Rhetticle/Ruthless-RFID/Firmware/Ruthless RFID/Core/Src/MFRC.c

/*
 * MFRC.c
 *
 *  Created on: Jan 30, 2024
 *      Author: rhett
 */


#include "MFRC.h"
#include "stm32f4xx.h"
#include "usbd_cdc_if.h"
#include "OLED.h"
#include "ruthlessfs.h"

extern I2C_HandleTypeDef hi2c1;



/* Write single byte MFRC register
 *
 * @param addr: register address
 *
 * @param data: value to write to register
 */

PCD_StatusTypeDef MFRC_REGW(uint8_t addr,uint8_t data){
	uint8_t value=data;
	if(HAL_I2C_Mem_Write(&hi2c1, MFRC_ADDR<<1, addr, 1, &value, 1, 100)!=HAL_OK){
		return(PCD_I2C_ERR);
	}
	else{
		return(PCD_OK);
	}
	HAL_Delay(1);
}

/* Read single byte from MFRC register
 *
 * @param addr: register address
 *
 * @param data: pointer to store read value
 */

PCD_StatusTypeDef MFRC_REGR(uint8_t addr,uint8_t* data){
	if(HAL_I2C_Mem_Read(&hi2c1, MFRC_ADDR<<1, addr, 1, data, 1, 100)!=HAL_OK){
		return(PCD_I2C_ERR);
	}
	else{
		return(PCD_OK);
	}
	HAL_Delay(1);
}

/* Write to MFRC FIFO buffer
 *
 * @param data: Array of data to write to FIFO
 *
 * @param size: Size of array (bytes)
 */

PCD_StatusTypeDef MFRC_FIFOW(uint8_t* data,uint8_t size){
	for(int i=0;i<size;i++){
		if(HAL_I2C_Mem_Write(&hi2c1, MFRC_ADDR<<1, 0x09, 1, &data[i], 1, 100)!=HAL_OK){
			return(PCD_I2C_ERR);

		}
		HAL_Delay(1);

	}
	return(PCD_OK);
}

/* Read from MFRC FIFO buffer
 *
 * @param data: Array to store read values (Ensure array is large enough)
 *
 * @param size: Number of bytes to read from FIFO
 */

PCD_StatusTypeDef MFRC_FIFOR(uint8_t* data,uint8_t size){
	for(int i=0;i<size;i++){
		if(HAL_I2C_Mem_Read(&hi2c1, MFRC_ADDR<<1, 0x09, 1, &data[i], 1, 100)!=HAL_OK){
			return(PCD_I2C_ERR);
		}
		HAL_Delay(1);

	}
	return(PCD_OK);
}

void MFRC_Test(void){
	uint8_t value;
	MFRC_REGR(0x37,&value); //Expect 0x91 or 0x92
	CDC_Transmit_FS(&value,1);
}

void MFRC_ANTON(void){
	uint8_t value;
	MFRC_REGR(TX_CONT, &value);
	if ((value & 0x03) != 0x03) {
		MFRC_REGW(TX_CONT, value | 0x03);
	}
}

void SET_ANTGAIN(void){
	uint8_t value;
	MFRC_REGR(RFCfgReg,&value);
	MFRC_REGW(RFCfgReg,value|0x70); //Set receiver gain to 48dB
}

void ClearBitMask(uint8_t addr,uint8_t mask){
	uint8_t tmp;
	MFRC_REGR(addr,&tmp);
	MFRC_REGW(addr,tmp&(~mask));
}

void MFRC_ANTOFF(void){
	ClearBitMask(TX_CONT,0x03);
}

/*
 * Function to calculate CRC on whatever data is in FIFO
 * !!CRCIRQ bit in DivIrqReg register can be used to detect when CRC has been calculated!!
 *
 * @param result: Array to store the two bytes of CRC
 *
 * */

PCD_StatusTypeDef CALC_CRC(uint8_t* data,uint8_t size,uint8_t* result){
	uint8_t CRCIRQ;
	MFRC_REGW(CMD_REG,IDLE); //clear command register
	MFRC_REGW(DIVIRQ,0x04); //Clear interrupt bits so we can detect when CRCIRQ is set
	MFRC_REGW(FIFO_LEV,0x80);
	MFRC_FIFOW(data, size); //Write data to FIFO ready for CRC calculation
	MFRC_REGW(CMD_REG,CALCCRC); //Execute CRC calculation command
	HAL_Delay(100);
	MFRC_REGR(DIVIRQ,&CRCIRQ);
	if((CRCIRQ&0x04)!=0x04){
		return(CRC_ERR); //CRC calculation took too long
	}
	MFRC_REGW(CMD_REG,IDLE);
	MFRC_REGR(CRCL, &result[0]);
	MFRC_REGR(CRCH, &result[1]); //Store the 16-bit CRC in result
	return(PCD_OK);

}

/* Initialise MFRC to begin transceiving
 *
 * Code is written to interface with MIFARE Ultralight PICC. Different PICCs will need different baud rate.
 */

PCD_StatusTypeDef MFRC_INIT(void){
	HAL_GPIO_WritePin(GPIOB, NRST, 1); //Make sure MFRC is not reset
	HAL_GPIO_WritePin(GPIOB, NRST, 0);
	HAL_Delay(1);
	HAL_GPIO_WritePin(GPIOB, NRST, 1);
	HAL_Delay(50);
	MFRC_REGW(TX_REG,0x00);
	MFRC_REGW(RX_REG,0x00);
	MFRC_REGW(MODWIDTH,0x26);
	MFRC_REGW(TXASK,0x40); //Force 100% ASK modulation regardless of ModGsPrereg
	MFRC_REGW(MODE_REG,0x3D);
	MFRC_ANTON();
	return(PCD_OK);



}


/* Transceive data between MFRC and PICC
 *
 * @param sendData: Array of data to send
 *
 * @param sendsize: Number of bytes to send
 *
 * @param recdata: Array to store received data
 *
 * @param recsize: Number of bytes to receive
 *
 * @param validbits: Number of valid bits within given byte in sendData
 *
 * !!Check PICC datasheet to see what data is needed in sendData i.e. Read/Write command, response bytes etc!!
 * !!When writing ensure correct address, most MIFARE PICCs contain OTP (one-time-programmable) sections as well as
 * lock bytes to remove write permissions from certain pages. These operations are NOT reversable!!
 */

PCD_StatusTypeDef MFRC_TRANSCEIVE(uint8_t* sendData,uint8_t sendsize,uint8_t* recdata,uint8_t recsize,uint8_t validbits){
	uint8_t IRQval=0;
	uint8_t BIT_val=0;

	MFRC_REGW(CMD_REG,IDLE); //Clear command register
	MFRC_REGW(IRQ_REG,0x7F);
	MFRC_REGW(FIFO_LEV,0x80); //Clear FIFO buffer
	MFRC_FIFOW(sendData,sendsize); //Write data to FIFO ready for transmission
	MFRC_REGW(BITFRAME,validbits);
	MFRC_REGW(CMD_REG,TRANSCEIVE); //Send FIFO data and receive PICC response
	MFRC_REGR(BITFRAME,&BIT_val);
	MFRC_REGW(BITFRAME,(BIT_val|0x80)); //Start send bit
	while(IRQval&0x30!=0x30){ //Hang here until RXIRQ and IDLEIRQ bits are set
		MFRC_REGR(IRQ_REG,&IRQval);
	}
	HAL_Delay(1);
	MFRC_FIFOR(recdata,recsize); //Read and store received data


	return(PCD_OK);
}

/*
 * Function to send a REQA to detect if a PICC is present
 *
 * @param response: Array to store response from PICC
 *
 * */

PCD_StatusTypeDef MFRC_REQA(uint8_t* response){
	uint8_t REQ=0x26;
	ClearBitMask(COLLREG, 0x80);
	if(MFRC_TRANSCEIVE(&REQ,1, response, 2, 7)!=PCD_OK){//REQA is a 7-bit command
		return(PCD_COMM_ERR);
	}

	else{
		return(PCD_OK);
	}
}

/*
 * Function to issue the WUPA command to PICC (We use this to go from HALT to READY state check ISO standard)
 *
 * @param reponse: PICC reponse to WUPA (Expect 0x44, 0x00 for ULTRALIGHT
 * */

PCD_StatusTypeDef MFRC_WUPA(uint8_t* response){
	uint8_t WUPA=0x52;
	ClearBitMask(COLLREG, 0x80);
	if(MFRC_TRANSCEIVE(&WUPA,1, response, 2, 7)!=PCD_OK){//WUPA is a 7-bit command
		return(PCD_COMM_ERR);
	}

	else{
		return(PCD_OK);
	}
}

/*
 * Function to issue HALTA command to PICC (Change from READY to HALT state) Send WUPA and select sequence to re-select PICC
 * */

PCD_StatusTypeDef MFRC_HALTA(void){
	uint8_t transaction[4]={ULTRA_HALTA,0x00};
	uint8_t CRC_val[2];
	uint8_t ack;

	if(CALC_CRC(transaction, 2, CRC_val)!=PCD_OK){
		return(CRC_ERR);
	}
	memcpy(transaction+2,CRC_val,2);

	if(MFRC_TRANSCEIVE(transaction, 4, &ack, 1, 0)!=PCD_OK){
		return(PCD_COMM_ERR);
	}

	else{
		return(PCD_OK);
	}
}

/*
 * Function to transceive anticollision cascade level 1 command (Second step after REQA to select PICC)
 *
 * @param response: Array to store PICC response to anticollision command
 * */

PCD_StatusTypeDef MFRC_ANTICOL1(uint8_t* reponse){
	uint8_t transaction[]={0x93,0x20};
	ClearBitMask(COLLREG, 0x80);
	if(MFRC_TRANSCEIVE(transaction, 2, reponse, 5, 0)!=PCD_OK){
		return(PCD_COMM_ERR);
	}
	else{
		return(PCD_OK);
	}
}

/*
 * Function to perform SELECT command (Cascade level 1)
 *
 * @param anticol: Data the is retrieved from MFRC_ANTICOL1
 *
 * @param response: Array to store PICC response to command (Expect SAK of 0x04 and two bytes CRC)
 *
 * */

PCD_StatusTypeDef MFRC_SEL1(uint8_t* anticol,uint8_t* response){
	uint8_t transaction[9]={0x93,0x70};
	uint8_t CRC_val[2];

	memcpy(transaction+2,anticol,5);
	CALC_CRC(transaction, 7, CRC_val);

	memcpy(transaction+7,CRC_val,2);

	if(MFRC_TRANSCEIVE(transaction, 9, response, 3, 0)!=PCD_OK){
		return(PCD_COMM_ERR);
	}

	else{
		return(PCD_OK);
	}

}

/*
 * Function to transceive anticollision cascade level 2 command (Cascade level 1 commands must be performed first)
 *
 * @param response: Array to store PICC response to anticollision command
 * */

PCD_StatusTypeDef MFRC_ANTICOL2(uint8_t* reponse){
	uint8_t transaction[]={0x95,0x20};
	ClearBitMask(COLLREG, 0x80);
	if(MFRC_TRANSCEIVE(transaction, 2, reponse, 5, 0)!=PCD_OK){
		return(PCD_COMM_ERR);
	}
	else{
		return(PCD_OK);
	}
}

/*
 * Function to perform SELECT command (Cascade level 2)
 *
 * @param anticol: Data the is retrieved from MFRC_ANTICOL2
 *
 * @param response: Array to store PICC response to command (Expect SAK of 0x00 and two bytes CRC)
 *
 * */

PCD_StatusTypeDef MFRC_SEL2(uint8_t* anticol,uint8_t* response){
	uint8_t transaction[9]={0x95,0x70};
	uint8_t CRC_val[2];

	memcpy(transaction+2,anticol,5);
	CALC_CRC(transaction, 7, CRC_val);

	memcpy(transaction+7,CRC_val,2);

	if(MFRC_TRANSCEIVE(transaction, 9, response, 3, 0)!=PCD_OK){
		return(PCD_COMM_ERR);
	}

	else{
		return(PCD_OK);
	}

}

/*
 * Function to select the MIFARE ULTRALIGHT PICC (Don't forget to call REQA on first power up or use PICC_CHECK below)
 * */

PCD_StatusTypeDef PICC_Select(void){
	  uint8_t ANTICOL1[5];
	  uint8_t SELECT1[3];
	  uint8_t ANTICOL2[5];
	  uint8_t SELECT2[3];
	  uint8_t ATQA[2];

	  if (PICC_CHECK() != PCD_OK) {
		  return PCD_COMM_ERR;
	  }
	  MFRC_WUPA(ATQA);
	  MFRC_ANTICOL1(ANTICOL1);
	  if(ANTICOL1[0]!=0x88){
		  return(PCD_COMM_ERR);
	  }
	  HAL_Delay(10);
	  MFRC_SEL1(ANTICOL1, SELECT1);
	  HAL_Delay(10);
	  MFRC_ANTICOL2(ANTICOL2);
	  HAL_Delay(10);
	  MFRC_SEL2(ANTICOL2, SELECT2);
	  HAL_Delay(10);
	  return(PCD_OK);
}

/*
 * Function to check for PICC in field
 * */

PCD_StatusTypeDef PICC_CHECK(void){
	uint8_t ATQA[2];
	if(MFRC_WUPA(ATQA)!=PCD_OK){
		return(PCD_COMM_ERR);
	}

	else{
		if((ATQA[0]!=ULTRA_ATQA0) || (ATQA[1] != ULTRA_ATQA1)){
			return(PCD_COMM_ERR);
		}
		else{
			MFRC_HALTA();
			return(PCD_OK);
		}
	}
}
/*
 * Function to read data from MIFARE ULTRALIGHT PICC
 *
 * @param addr: Start address (PICC will return data from first four pages)
 *
 * @param data: Array to store read data
 *
 * */

PCD_StatusTypeDef UL_READ(uint8_t addr,uint8_t* data){

	uint8_t transaction[4]={ULTRA_READ,addr};
	uint8_t CRC_val[2];

	CALC_CRC(transaction, 2, CRC_val);

	memcpy(transaction+2,CRC_val,2);

	if(MFRC_TRANSCEIVE(transaction, 4, data, UL_READSIZE, 0)!=PCD_OK){
		return(PCD_COMM_ERR);
	}

	else{
		return(PCD_OK);
	}
}

/*
 * Function to write 4 bytes (1 page) to MIFARE Ultralight PICC
 *
 * @param addr: Page start address
 *
 * @param data: Array of 4 bytes to write
 *
 * */

PCD_StatusTypeDef UL_WRITE(uint8_t addr,uint8_t* data){
	uint8_t transaction[8]={ULTRA_WRITE,addr};
	uint8_t ack;
	uint8_t CRC_val[2];

	//Safety check to see if we're trying to write to any of the first four pages which contain sensitive data (uid, OTP etc)
	if (addr <= 3) {
		return PCD_PROTECTED_ERR;
	}

	memcpy(transaction+2,data,4);

	CALC_CRC(transaction, 6, CRC_val);

	memcpy(transaction+6,CRC_val,2);

	if(MFRC_TRANSCEIVE(transaction, 8, &ack, 1, 0)!=PCD_OK){
		return(PCD_COMM_ERR);
	}

	else{
		return(PCD_OK);
	}
}

void USB_print(char* mess){
	char send[strlen(mess) + 1];
	strcpy(send, mess);

	CDC_Transmit_FS((uint8_t*)send, strlen(mess));
	HAL_Delay(10);
}

/**
 * Read the 7 byte uid of MIFARE Ultralight card
 *
 * @param uid - Array to store uid
 * @return PCD_OK if uid was successfully read
 * */
PCD_StatusTypeDef UL_getuid(uint8_t* uid) {
	uint8_t read[UL_READSIZE];

	if (UL_READ(0x00, read) != PCD_OK) {
		return PCD_COMM_ERR;
	}

	memcpy(uid, read, UL_UIDPART1);
	memcpy(uid + UL_UIDPART1, read + UL_UIDPART2, UL_UIDPART2);
	return PCD_OK;
}

/**
 * Read uid into a string format
 *
 * @param uid - Array to store string representation of string
 * @return PCD_OK if uid was successfully read
 * */
PCD_StatusTypeDef UL_getuidstr(char* uid_str) {
	uint8_t uid[UL_UIDSIZE];

	if (UL_getuid(uid) != PCD_OK) {
		return PCD_COMM_ERR;
	}

	sprintf(uid_str, "%X%X%X%X%X%X%X", uid[0], uid[1], uid[2], uid[3], uid[4], uid[5], uid[6]);
	return PCD_OK;
}

/**
 * Get all 64 bytes of user data from card
 *
 * @param data - Array to store data
 * @return PCD_OK if data was successfully read
 * */
PCD_StatusTypeDef UL_getalldata(uint8_t* data) {

	for (int i = 0; i < UL_DATAEND; i += UL_PAGESIZE) {
		if (UL_READ(i, data) != PCD_OK) {
			return PCD_COMM_ERR;
		}
		data += UL_READSIZE; //increment pointer
	}

	return PCD_OK;
}

/**
 * Read MIFARE Ultralight card data into card struct
 *
 * !!Name of card is set by user after being read!!
 *
 * @param result - Card to store data into
 * @return PCD_OK if data was successfully read
 * */
PCD_StatusTypeDef UL_readcard(Card* result) {

	result->type = "MIFARE Ultralight";
	result->uidsize = UL_UIDSIZE;
	result->contents_size = UL_MEMSIZE;
	result->read_protected = 0;

	if (PICC_Select() != PCD_OK) { //Select PICC if available
		return PCD_NO_PICC;
	}
	if ((UL_getuid(result->uid) != PCD_OK) || (UL_getalldata(result->contents) !=  PCD_OK)) {
		return PCD_COMM_ERR;
	}
	return PCD_OK;
}

/**
 * Write a card object to a physical card
 * @param towrite - Card instance to write
 * @return PCD_OK if card was successfully written to and verified.
 * */
PCD_StatusTypeDef UL_writecard(Card* towrite) {
	uint8_t* data_to_write = malloc(UL_DATASIZE * sizeof(uint8_t));
	memcpy(data_to_write, towrite->contents + (UL_MEMSIZE - UL_DATASIZE), UL_DATASIZE);

	if (PICC_Select() != PCD_OK) {
		free(data_to_write);
		return PCD_NO_PICC;
	}

	for (int addr = UL_DATASTART; addr <= UL_DATAEND; addr++) {
		if (UL_WRITE(addr, data_to_write + (UL_PAGESIZE * (addr - UL_DATASTART))) != PCD_OK) {
			free(data_to_write);
			return PCD_COMM_ERR;
		}
	}
	free(data_to_write);
	return PCD_OK;
}

/**
 * Convert a uid to a string
 *
 * @param uid - Uid
 * @param size - Size of uid
 * @return pointer to string of uid
 * */
char* uid_tostring(uint8_t* uid, uint8_t size) {
	char* result = malloc((2 * size * sizeof(char)) + 1); //multiply by 2 since 1 byte is two hex digits

	for (int i = 0; i < size; i++) {
		if (uid[i] <= 0x0F) { //Only one hex character
			sprintf(result + (2 * i), "0%X", uid[i]);
		} else {
			sprintf(result + (2 * i), "%X", uid[i]);
		}
	}
	result[2 * size] = '\0'; //Add null
	return result;
}

/**
 * Verify that a phyiscal card's contents matches what was intended to be written
 * @param check - Card to check phyiscal card data against
 * @return PCD_OK if contents is correct
 * */
PCD_StatusTypeDef UL_verify(Card* check) {
	Card* read = malloc(sizeof(Card));
	read->contents = malloc(UL_MEMSIZE * sizeof(uint8_t));
	read->uid = malloc(UL_UIDSIZE * sizeof(uint8_t));

	if (UL_readcard(read) != PCD_OK) {
		free(read->contents);
		free(read->uid);
		free(read);
		return PCD_COMM_ERR;
	}

	for (int byte = UL_USERSTART; byte < UL_MEMSIZE; byte++) {
		if (read->contents[byte] != check->contents[byte]) {
			free(read->contents);
			free(read->uid);
			free(read);
			return PCD_VERIFY_ERR;
		}
	}
	free(read->contents);
	free(read->uid);
	free(read);
	return PCD_OK;
}

/**
 * Print relevant info of card to terminal over USB
 * @param card - Card to print details of
 * @param pagesize - Number of bytes in each page of memory for given card
 * @return PCD_OK if card details were successfully printed
 * */
PCD_StatusTypeDef dump_card_serial (Card* card, uint8_t pagesize) {
	char* uid = uid_tostring(card->uid, card->uidsize);

	printf("Type: %s\r\n", card->type);
	printf("UID: %s\r\n", uid);
	printf("Page    Byte\r\n");
	free(uid);

	printf("     "); //filler
	for (int i = 0; i < pagesize; i++) {
		printf("%i  ", i);
	}
	printf("\r\n");

	for (int i = 0; i < card->contents_size/pagesize; i++) {
		printf("%i    ", i);
		for (int j = 0; j < pagesize; j++) {
			if (card->contents[(i * pagesize) + j] <= 0xF) {
				printf("0%X ", card->contents[(i * pagesize) + j]);
			} else {
				printf("%X ", card->contents[(i * pagesize) + j]);
			}

		}
		printf("\r\n");
	}
	return PCD_OK;
}
