Rhetticle/Ruthless-RFID/Firmware/Ruthless RFID/Core/Inc/OLED.h

/*
 * OLED.h
 *
 *  Created on: Jan 29, 2024
 *      Author: rhett
 */

#ifndef INC_OLED_H_
#define INC_OLED_H_

#include <stm32f4xx.h>
#include "screen.h"

#define OLED_CS GPIO_PIN_4
#define OLED_RST GPIO_PIN_3
#define OLED_DC GPIO_PIN_1 //Port B

#define NORMAL 0
#define INVERT 1
#define OLED_LEFT 0
#define OLED_RIGHT 1
#define OLED_NORESTORE 0
#define OLED_RESTORE 1

//Character constants
#define OLED_CHARSIZE 5 //Character is 5 columns wide
#define OLED_INVCHARSIZE 7 //Inverted character is 7 columns wide
#define ASCII_START 0x20

//File related constants
#define FILES_PERSCREEN 3

//Display settings constants
#define CONTRAST_STEPSIZE 50

//Commands
#define LOWER_COL 0x02 //Lower nibble op code for column start (0x02)
#define UPPER_COL 0x10 //Upper nibble op code of column start (0x02)
#define CHRG_PMP 0x33 //Set Charge pump output to 9V
#define LINE_STRT 0x40 //Start at line 0x00
#define CNTRST_SET 0x81 //Op code for changing contrast
#define CNTRST 0xFF //Max constrast
#define SEG_MAP 0xA1 //Left rotate
#define DISP_NORM 0xA6
#define DISP_INV 0xA7
#define MUX_SET 0xA8
#define MUX 0x3F
#define DCDC_SET 0xAD
#define DCDC 0x8B
#define DISP_ON 0xAF
#define DISP_OFF 0xAE
#define PAGE_ADDR 0xB0
#define SCAN_DIR 0xC8 //COM[n-1] to COM0
#define DISP_OFFSET_SET 0xD3
#define DISP_OFFSET 0x00
#define OSC_SET 0xD5
#define OSC 0x80 //+15% on top of default internal clock speed
#define PRE_CHRG_SET 0xD9
#define PRE_CHRG 0x1F
#define COM_SET 0xDA
#define COM 0x12
#define VCOM_SET 0xDB
#define VCOM 0x40
#define NOP 0xE3

static const char ASCII[96][5] = {
 {0x00, 0x00, 0x00, 0x00, 0x00} // 20  (space)
,{0x00, 0x00, 0x5f, 0x00, 0x00} // 21 !
,{0x00, 0x07, 0x00, 0x07, 0x00} // 22 "
,{0x14, 0x7f, 0x14, 0x7f, 0x14} // 23 #
,{0x24, 0x2a, 0x7f, 0x2a, 0x12} // 24 $
,{0x23, 0x13, 0x08, 0x64, 0x62} // 25 %
,{0x36, 0x49, 0x55, 0x22, 0x50} // 26 &
,{0x00, 0x05, 0x03, 0x00, 0x00} // 27 '
,{0x00, 0x1c, 0x22, 0x41, 0x00} // 28 (
,{0x00, 0x41, 0x22, 0x1c, 0x00} // 29 )
,{0x14, 0x08, 0x3e, 0x08, 0x14} // 2a *
,{0x08, 0x08, 0x3e, 0x08, 0x08} // 2b +
,{0x00, 0x50, 0x30, 0x00, 0x00} // 2c ,
,{0x08, 0x08, 0x08, 0x08, 0x08} // 2d -
,{0x00, 0x60, 0x60, 0x00, 0x00} // 2e .
,{0x20, 0x10, 0x08, 0x04, 0x02} // 2f /
,{0x3e, 0x51, 0x49, 0x45, 0x3e} // 30 0
,{0x00, 0x42, 0x7f, 0x40, 0x00} // 31 1
,{0x42, 0x61, 0x51, 0x49, 0x46} // 32 2
,{0x21, 0x41, 0x45, 0x4b, 0x31} // 33 3
,{0x18, 0x14, 0x12, 0x7f, 0x10} // 34 4
,{0x27, 0x45, 0x45, 0x45, 0x39} // 35 5
,{0x3c, 0x4a, 0x49, 0x49, 0x30} // 36 6
,{0x01, 0x71, 0x09, 0x05, 0x03} // 37 7
,{0x36, 0x49, 0x49, 0x49, 0x36} // 38 8
,{0x06, 0x49, 0x49, 0x29, 0x1e} // 39 9
,{0x00, 0x36, 0x36, 0x00, 0x00} // 3a :
,{0x00, 0x56, 0x36, 0x00, 0x00} // 3b ;
,{0x08, 0x14, 0x22, 0x41, 0x00} // 3c <
,{0x14, 0x14, 0x14, 0x14, 0x14} // 3d =
,{0x00, 0x41, 0x22, 0x14, 0x08} // 3e >
,{0x02, 0x01, 0x51, 0x09, 0x06} // 3f ?
,{0x32, 0x49, 0x79, 0x41, 0x3e} // 40 @
,{0x7e, 0x11, 0x11, 0x11, 0x7e} // 41 A
,{0x7f, 0x49, 0x49, 0x49, 0x36} // 42 B
,{0x3e, 0x41, 0x41, 0x41, 0x22} // 43 C
,{0x7f, 0x41, 0x41, 0x22, 0x1c} // 44 D
,{0x7f, 0x49, 0x49, 0x49, 0x41} // 45 E
,{0x7f, 0x09, 0x09, 0x09, 0x01} // 46 F
,{0x3e, 0x41, 0x49, 0x49, 0x7a} // 47 G
,{0x7f, 0x08, 0x08, 0x08, 0x7f} // 48 H
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
}; // end char ASCII[96][5]

extern SPI_HandleTypeDef hspi1; //Our SPI bus connected to OLED

void OLED_OFF(void);
HAL_StatusTypeDef OLED_cmd(uint8_t data);
HAL_StatusTypeDef OLED_INIT(void);
HAL_StatusTypeDef OLED_data(uint8_t* data,uint8_t size);
void OLED_PWRDWN(void);
void OLED_Test(void);
void OLED_FLUSH(uint8_t* mem);
void OLED_InvChar(char character,uint8_t* result);
void OLED_drawChar(uint8_t page,uint8_t col, char character,uint8_t invert);
void OLED_Printlin(uint8_t page,uint8_t col,char* string,uint8_t invert);
void OLED_Shift(uint8_t page,uint8_t start_col,uint8_t spaces, uint8_t dir, char* string);
void OLED_PrintCent(uint8_t page, char* string, uint8_t invert);
void OLED_Print(char* string);
void OLED_SCREEN(const Screen* screen,uint8_t invert);
void OLED_SCRNREF(const Screen* screen,uint8_t dataindx,char* data);
void OLED_FILL(uint8_t* data,uint8_t page,uint8_t start_col, uint8_t length);
void OLED_SELECT(const Screen* screen,uint8_t selopt,int restore);
void OLED_select_inv(const Screen* screen, uint8_t selopt);
HAL_StatusTypeDef OLED_display_files(const Screen* screen, uint8_t page);
uint8_t find_restore_string(const Screen* screen, uint8_t prev_sel_opt);
void oled_show_file(uint16_t entry);
void oled_move_selection(const Screen* screen, uint8_t* arrow_index, uint8_t restore);
void oled_move_selection_inv(const Screen* screen, uint8_t* select_index);
void oled_keyboard_insertChar (uint8_t char_index_selected, char** curr_name);
void oled_keyboard_removeChar (char** curr_name);
void oled_set_contrast (uint8_t value);
void oled_show_stats(void);
#endif /* INC_OLED_H_ */
