Rhetticle/Ruthless-RFID/Firmware/Ruthless RFID/Core/Src/screen.c

/*
 * screen.c
 *
 *  Created on: Jun 11, 2024
 *      Author: rhett
 */
#include "OLED.h"
#include "screen.h"
#include "stdint.h"

static const char* HOME_SCREEN[7]={"Ruthless RFID","1.READ CARD","2.WRITE CARD","3.SHOW FILES","4.CLONE","5.DISP","6.STATS"};
static const uint8_t HOME_DATLOC[7][2]={{0,0},{2,START_COL},{4,START_COL},{6,START_COL},{2,MID_COL+15},{4,MID_COL+15},{6,MID_COL+15}};
static const uint8_t HOME_SEL[6][2]={{2,START_COL},{4,START_COL},{6,START_COL},{2,MID_COL+15},{4,MID_COL+15},{6,MID_COL+15}}; //Select arrow info for HOME screen format {Page,column,replacesize}}

static const char* READ_SCREEN[3]={"READ CARD","STANDARD: ISO 14443","STATUS: NO CARD"};
static const uint8_t READ_DATLOC[3][2]={{0,0},{2,START_COL},{4,START_COL}};
static const uint8_t READ_SEL[1][2]={{0,0}};

static const char* CARD_FOUNDSCREEN[5]={"CARD FOUND","UID: ","IC: ","SAVE","EXIT"};
static const uint8_t CARD_FOUNDATLOC[5][2]={{0,0},{2,START_COL},{4,START_COL},{7,START_COL+12},{7,END_COL-24}};
static const uint8_t CARD_FOUNDSEL[2][2]={{7,START_COL},{7,END_COL-36}};

static const char* WRITE_SCREEN[4]={"WRITE CARD","STANDARD: ISO 14443","SRC FILE: ","STATUS: NO CARD"};
static const uint8_t WRITE_DATLOC[4][2]={{0,0},{2,START_COL},{4,START_COL},{6,START_COL}};
static const uint8_t WRITE_SEL[1][2] = {{0,0}};

static const char* SHOW_FILESSCREEN[8] = {"FILES", "* ", "* ", "* ", "FREE: ", "USED: ", "  NEXT", "EXIT"};
static const uint8_t SHOW_DATLOC[8][2] = {{0,0},{2,START_COL},{4,START_COL},{6,START_COL},{2,MID_COL},{4,MID_COL}, {6,MID_COL - 12}, {6, END_COL - 24}};
static const uint8_t SHOW_SEL[5][2] = {{2, START_COL}, {4,START_COL}, {6, START_COL}, {6, MID_COL-12}, {6, END_COL - 36}};

static const char* FILEDATA_SCREEN[5] = {".", "IC:", "UID: ", "DELETE", "EXIT"};
static const uint8_t FILEDATA_DATLOC[5][2] = {{0,MID_COL-12}, {2,START_COL},{4,START_COL},{6,START_COL + 12}, {6, END_COL - 24}};
static const uint8_t FILEDATA_SEL[2][2] = {{6, START_COL},{6,END_COL - 36}};

static const char* CLONE_SCREEN[4] = {"CLONE", "STANDARD: ISO 14443", "PLACE CARD YOU WISH", "TO COPY FROM"};
static const uint8_t CLONE_DATLOC[4][2] = {{0,0}, {2, START_COL}, {4, START_COL}, {6, START_COL}};
static const uint8_t CLONE_SEL[1][2] = {{0,0}};

static const char* KEYBOARD_SCREEN[29] = {" ", "A", "B", "C", "D", "E", "F", "G", "H", "I", "J", "K", "L", "M",
										"N", "O", "P", "Q", "R", "S", "T", "U", "V", "W", "X", "Y", "Z", "DEL", "ENTER"};
static const uint8_t KEYBOARD_DATLOC[29][2] = {{0,MID_COL - 12}, {2, START_COL}, {2, START_COL + 12}, {2, START_COL + 24}, {2, START_COL + 36},
											{2, START_COL + 48}, {2, START_COL + 60}, {2, START_COL + 72}, {2, START_COL + 84}, {2, START_COL + 96},
											{2, START_COL + 108}, {2, START_COL + 120}, {4, START_COL}, {4, START_COL + 12}, {4, START_COL + 24},
											{4, START_COL + 36}, {4, START_COL +48}, {4, START_COL + 60}, {4, START_COL + 72},
											{4, START_COL + 84}, {4, START_COL + 96}, {4, START_COL + 108}, {4, START_COL + 120},{6, START_COL},
											{6, START_COL + 12}, {6, START_COL + 24}, {6, START_COL + 36}, {6, START_COL + 48}, {6, START_COL + 84}};

static const uint8_t KEYBOARD_SEL[28][2] = {{2, START_COL}, {2, START_COL + 12}, {2, START_COL + 24}, {2, START_COL + 36},
											{2, START_COL + 48}, {2, START_COL + 60}, {2, START_COL + 72}, {2, START_COL + 84}, {2, START_COL + 96},
											{2, START_COL + 108}, {2, START_COL + 120}, {4, START_COL}, {4, START_COL + 12}, {4, START_COL + 24},
											{4, START_COL + 36}, {4, START_COL +48}, {4, START_COL + 60}, {4, START_COL + 72},
											{4, START_COL + 84}, {4, START_COL + 96}, {4, START_COL + 108}, {4, START_COL + 120},{6, START_COL},
											{6, START_COL + 12}, {6, START_COL + 24}, {6, START_COL + 36}, {6, START_COL +48}, {6, START_COL + 84}};

static const char* DISP_SCREEN [5] = {"DISPLAY", "CONTRAST: ", "+", "-", "EXIT"};
static const uint8_t DISP_DATLOC [5][2] = {{0,0}, {2, START_COL}, {2, MID_COL}, {2, MID_COL + 24}, {7, END_COL - 24}};
static const uint8_t DISP_SEL [3][2] = {{2, MID_COL}, {2, MID_COL + 24}, {7, END_COL - 24}};

static const char* STATS_SCREEN [4] = {"STATS", "WRITES: ", "READS: ", "EXIT"};
static const uint8_t STATS_DATLOC [4][2] = {{0,0}, {2, START_COL}, {4, START_COL}, {7, END_COL - 24}};
static const uint8_t STATS_SEL [1][2] = {{7, END_COL - 36}};

/**
 * Screens
 *
 * */

//Home screen
const Screen SCRN_Home = {
		.datsize = sizeof(HOME_SCREEN)/sizeof(HOME_SCREEN[0]),
		.selsize = sizeof(HOME_SEL)/sizeof(HOME_SEL[0]),
		.data = HOME_SCREEN,
		.dataloc = HOME_DATLOC,
		.seldata = HOME_SEL,
};

//Read card
const Screen SCRN_ReadCard = {
		.datsize = sizeof(READ_SCREEN)/sizeof(READ_SCREEN[0]),
		.selsize = sizeof(READ_SEL)/sizeof(READ_SEL[0]),
		.data = READ_SCREEN,
		.dataloc = READ_DATLOC,
		.seldata = READ_SEL,
};

//Card found
const Screen SCRN_CardFound = {
		.datsize = sizeof(CARD_FOUNDSCREEN)/sizeof(CARD_FOUNDSCREEN[0]),
		.selsize = sizeof(CARD_FOUNDSEL)/sizeof(CARD_FOUNDSEL[0]),
		.data = CARD_FOUNDSCREEN,
		.dataloc = CARD_FOUNDATLOC,
		.seldata = CARD_FOUNDSEL,
};

const Screen SCRN_WriteCard = {
		.datsize = sizeof(WRITE_SCREEN)/sizeof(WRITE_SCREEN[0]),
		.selsize = sizeof(WRITE_SEL)/sizeof(WRITE_SEL[0]),
		.data = WRITE_SCREEN,
		.dataloc = WRITE_DATLOC,
		.seldata = WRITE_SEL,
};

//Show Files
const Screen SCRN_ShowFiles = {
		.datsize = sizeof(SHOW_FILESSCREEN)/sizeof(SHOW_FILESSCREEN[0]),
		.selsize = sizeof(SHOW_SEL)/sizeof(SHOW_SEL[0]),
		.data = SHOW_FILESSCREEN,
		.dataloc = SHOW_DATLOC,
		.seldata = SHOW_SEL,
};

//Show File contents
const Screen SCRN_FileData = {
		.datsize = sizeof(FILEDATA_SCREEN)/sizeof(FILEDATA_SCREEN[0]),
		.selsize = sizeof(FILEDATA_SEL)/sizeof(FILEDATA_SEL[0]),
		.data = FILEDATA_SCREEN,
		.dataloc = FILEDATA_DATLOC,
		.seldata = FILEDATA_SEL,
};

//Clone card
const Screen SCRN_Clone = {
		.datsize = sizeof(CLONE_SCREEN)/sizeof(CLONE_SCREEN[0]),
		.selsize = sizeof(CLONE_SEL)/sizeof(CLONE_SEL[0]),
		.data = CLONE_SCREEN,
		.dataloc = CLONE_DATLOC,
		.seldata = CLONE_SEL,
};

//Keyboard
const Screen SCRN_Keyboard = {
		.datsize = sizeof(KEYBOARD_SCREEN)/sizeof(KEYBOARD_SCREEN[0]),
		.selsize = sizeof(KEYBOARD_SEL)/sizeof(KEYBOARD_SEL[0]),
		.data = KEYBOARD_SCREEN,
		.dataloc = KEYBOARD_DATLOC,
		.seldata = KEYBOARD_SEL,
};

//Display settings
const Screen SCRN_Display = {
		.datsize = sizeof(DISP_SCREEN)/sizeof(DISP_SCREEN[0]),
		.selsize = sizeof(DISP_SEL)/sizeof(DISP_SEL[0]),
		.data = DISP_SCREEN,
		.dataloc = DISP_DATLOC,
		.seldata = DISP_SEL,
};

//Stats
const Screen SCRN_Stats = {
		.datsize = sizeof(STATS_SCREEN)/sizeof(STATS_SCREEN[0]),
		.selsize = sizeof(STATS_SEL)/sizeof(STATS_SEL[0]),
		.data = STATS_SCREEN,
		.dataloc = STATS_DATLOC,
		.seldata = STATS_SEL,
};
