Rhetticle/Ruthless-RFID/Firmware/Ruthless RFID/Core/Inc/terminal.h

/*
 * terminal.h
 *
 *  Created on: Jul 1, 2024
 *      Author: rhett
 */

#ifndef INC_TERMINAL_H_
#define INC_TERMINAL_H_

typedef enum {
	FG_BLACK = 30,
	FG_RED = 31,
	FG_GREEN = 32,
	FG_YELLOW= 33,
	FG_BLUE = 34,
	FG_MAGENTA = 35,
	FG_CYAN = 36,
	FG_WHITE = 37,
	FG_BRIGHTGREEN = 92,
	FG_BRIGHTYELLOW = 93,
	FG_BRIGHTCYAN = 96,
	FG_BRIGHTMAGENTA = 95,
	BG_BLACK = 40,
	BG_RED = 41,
	BG_GREEN = 42,
	BG_YELLOW = 43,
	BG_BLUE = 44,
	BG_MAGENTA = 45,
	BG_CYAN = 46,
	BG_WHITE = 47
}TerminalColour;

static const char* RR_TERMINALART[] = {
		 "_____       _   _     _                 _____  ______ _____ _____" ,
		 "|  __ \\     | | | |   | |               |  __ \\|  ____|_   _|  __ \\ ",
		 "| |__) |   _| |_| |__ | | ___  ___ ___  | |__) | |__    | | | |  | | ",
		 "|  _  / | | | __| '_ \\| |/ _ \\/ __/ __| |  _  /|  __|   | | | |  | | ",
		 "| | \\ \\ |_| | |_| | | | |  __/\\__ \\__ \\ | | \\ \\| |     _| |_| |__| | ",
		 "|_|  \\_\\__,_|\\__|_| |_|_|\\___||___/___/ |_|  \\_\\_|    |_____|_____/ "};
void terminal_init(void);
void move_terminal_cursor(int x, int y);
void clear_terminal(void);
void clear_to_end_of_line(void);
void set_colour (TerminalColour colour);

#endif /* INC_TERMINAL_H_ */
